Zeder-pathfinder/keyboard_project/atmega32U4-edition/PCB电路图/Schematic_netrunner42 v1.1_2023-11-26.png

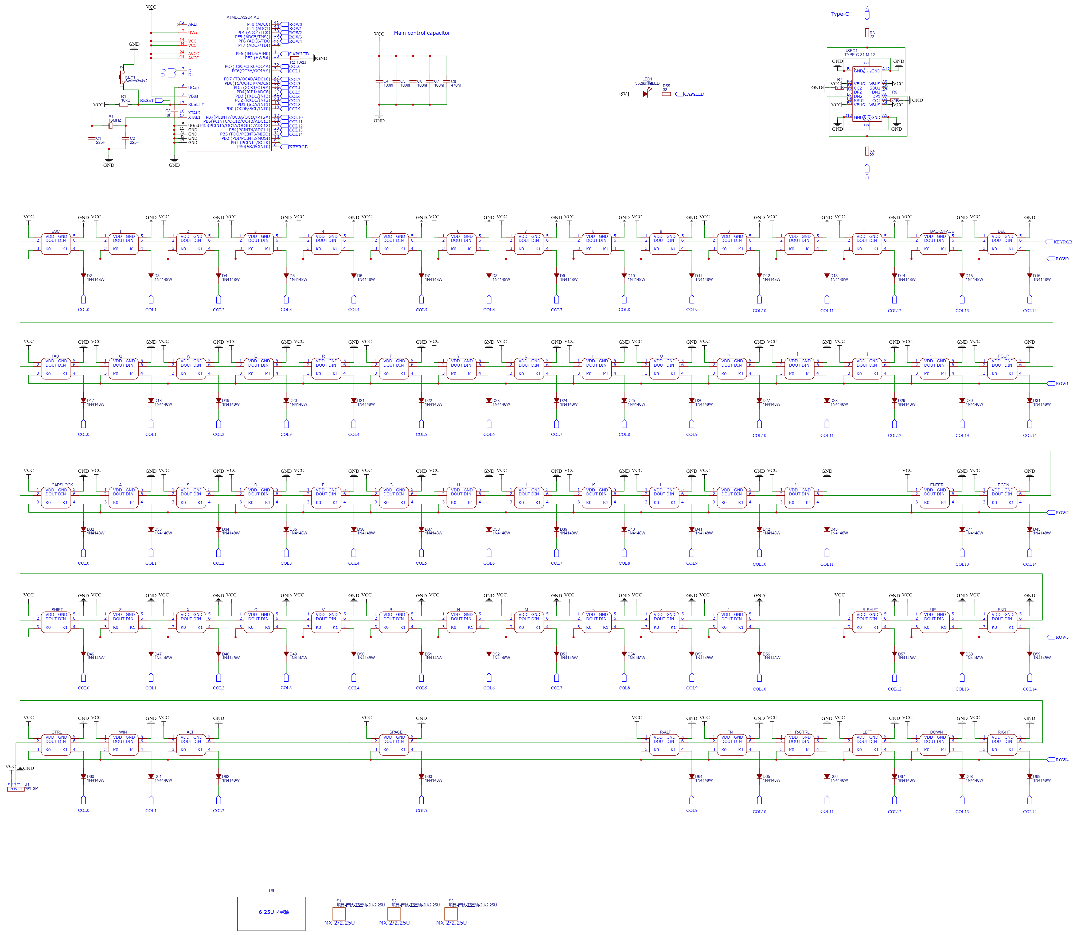
atmega32U4-edition/PCB电路图/Schematic_netrunner42 v1.1_2023-11-26.png
