Zeder-pathfinder/keyboard_project/atmega32U4-edition/PCB电路图/图片1.png

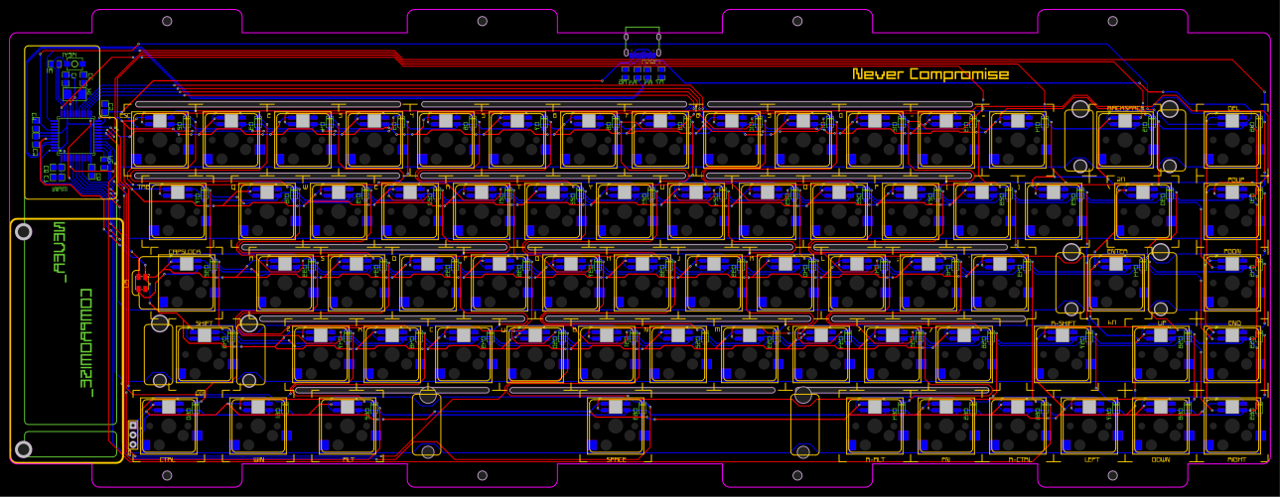
atmega32U4-edition/PCB电路图/图片1.png
