Zeder-pathfinder/keyboard_project/keyboard.jpg

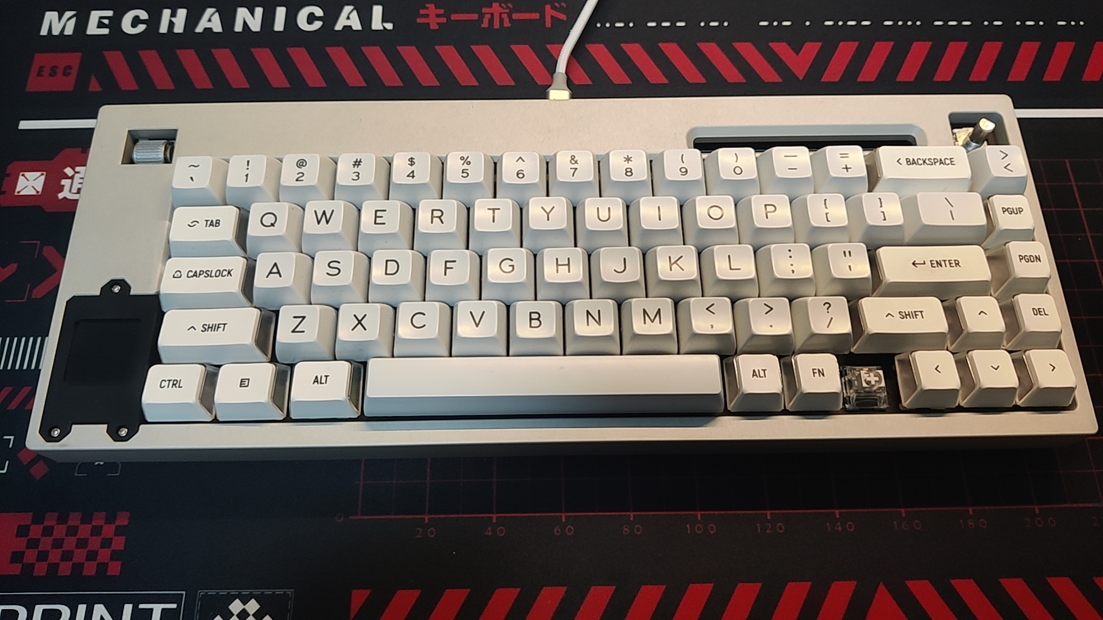
keyboard.jpg
