Zeder-pathfinder/keyboard_project/keyboard_model/render/rander1.png

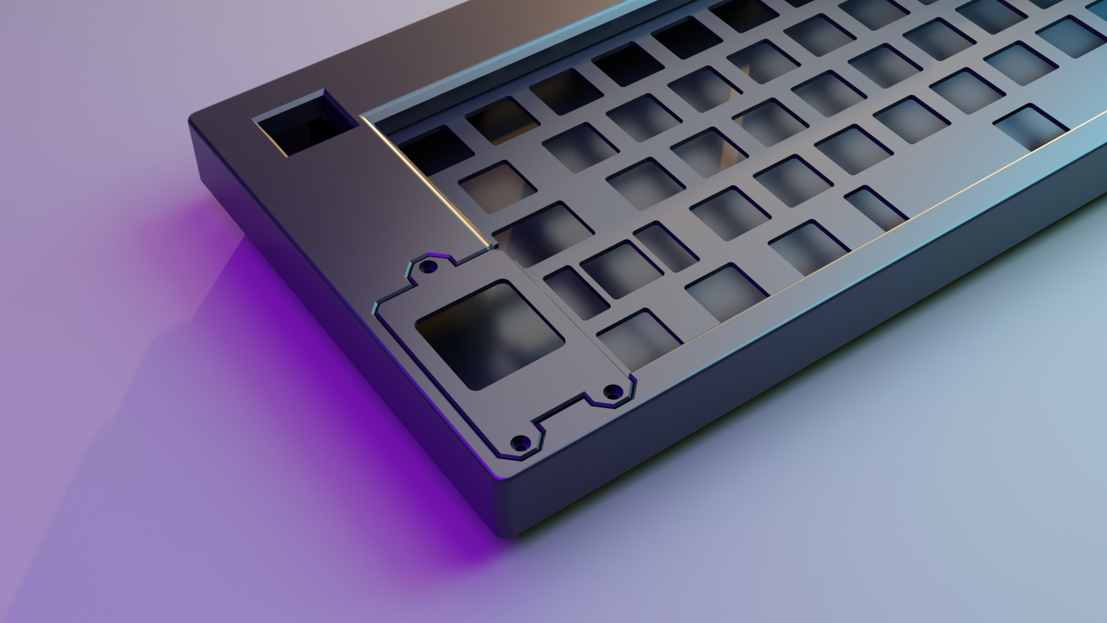
keyboard_model/render/rander1.png
