Zeder-pathfinder/keyboard_project/keyboard_model/render/rander2.png

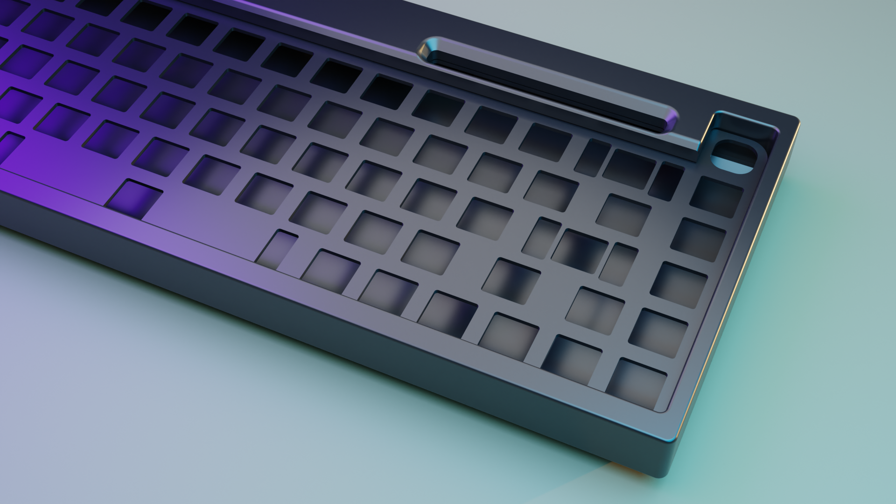
keyboard_model/render/rander2.png
