Zeder-pathfinder/keyboard_project/keyboard_model/render/rander3.png

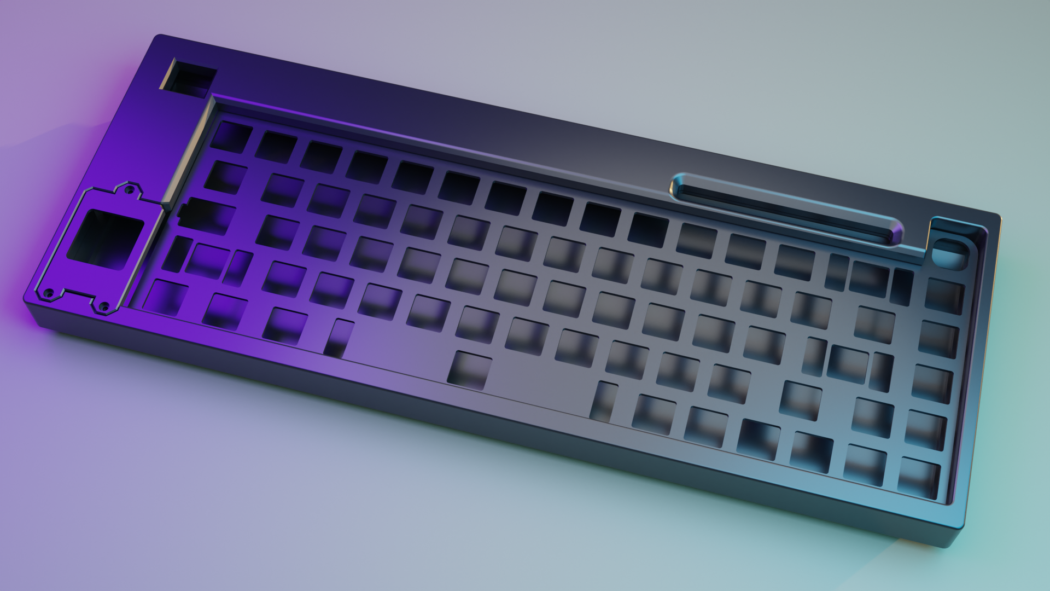
keyboard_model/render/rander3.png
