Zeder-pathfinder/keyboard_project/keyboard_model/render/rander4.png

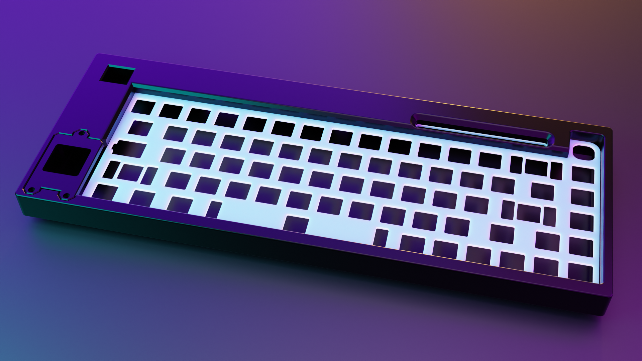
keyboard_model/render/rander4.png
