Zeder-pathfinder/keyboard_project/keyboard_model/Screw hole design/4holes_inside_base.png

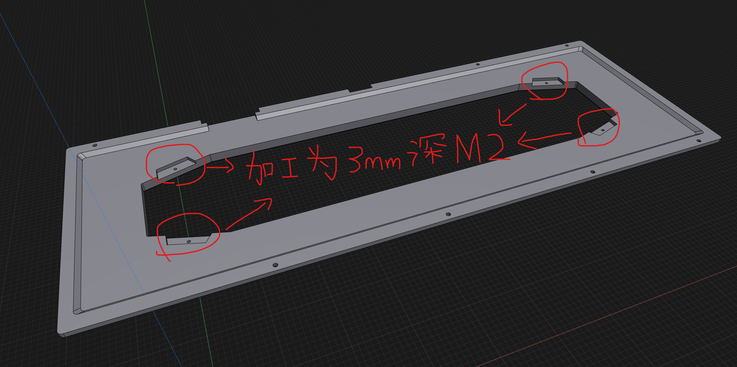
keyboard_model/Screw hole design/4holes_inside_base.png
